spqr/umichmoo/sensor.h

#ifndef SENSOR_CONF_H
#define SENSOR_CONF_H

#include "mymoo.h"

#if ENABLE_SESSIONS
#include "sessions.h"
#endif

#include <inttypes.h>
#include "sensor_api.h"


void init_sensors();


#if SIMPLE_QUERY_ACK
#define ENABLE_READS                  0
#define READ_SENSOR                   0
#endif
#if SENSOR_DATA_IN_ID
#define ENABLE_READS                  0
#define READ_SENSOR                   1
#endif
#if SIMPLE_READ_COMMAND
#define ENABLE_READS                  1
#define READ_SENSOR                   0
#endif
#if SENSOR_DATA_IN_READ_COMMAND
#define ENABLE_READS                  1
#define READ_SENSOR                   1
#endif

#endif //SENSOR_CONF_H
