spqr/umichmoo/sensors/quick_accel/quick_accel_sensor.h

/* See license.txt for license information. */

// these bit definitions are specific to Moo 1.0

#ifndef __QUICK_ACCEL_SENSOR_
#define __QUICK_ACCEL_SENSOR_

#define SENSOR_DATA_TYPE_ID       0x0B

#define ACCEL_ENABLE_BIT          BIT4   // 1.4
#define SET_ACCEL_ENABLE_DIR      P1DIR |= ACCEL_ENABLE_BIT
#define CLEAR_ACCEL_ENABLE_DIR    P1DIR &= ~ACCEL_ENABLE_BIT
#define TURN_ON_ACCEL_ENABLE      P1OUT |= ACCEL_ENABLE_BIT
#define TURN_OFF_ACCEL_ENABLE     P1OUT &= ~ACCEL_ENABLE_BIT

#define DATA_LENGTH_IN_WORDS      3
#define DATA_LENGTH_IN_BYTES      (DATA_LENGTH_IN_WORDS*2)

extern unsigned char sensor_busy;

#endif
