spqr/umichmoo/states.h

/* See license.txt for license information. */

#ifndef STATES_H
#define STATES_H

#define STATE_READY               0
#define STATE_ARBITRATE           1
#define STATE_REPLY               2
#define STATE_ACKNOWLEDGED        3
#define STATE_OPEN                4
#define STATE_SECURED             5
#define STATE_KILLED              6
#define STATE_READ_SENSOR         7

#endif
