spqr/umichmoo/version.h

#ifndef __MOO_VERSION_H__
#define __MOO_VERSION_H__

#define MOO1_1                        0x11
#define MOO1_2                        0x12
#define MOO1_2_1                      0x13

#endif /* __MOO_VERSION_H__ */
